eyasudev/-msft_button/ReadmeFiles/hardware-connection-images/hardware-camera-signal-1.jpeg

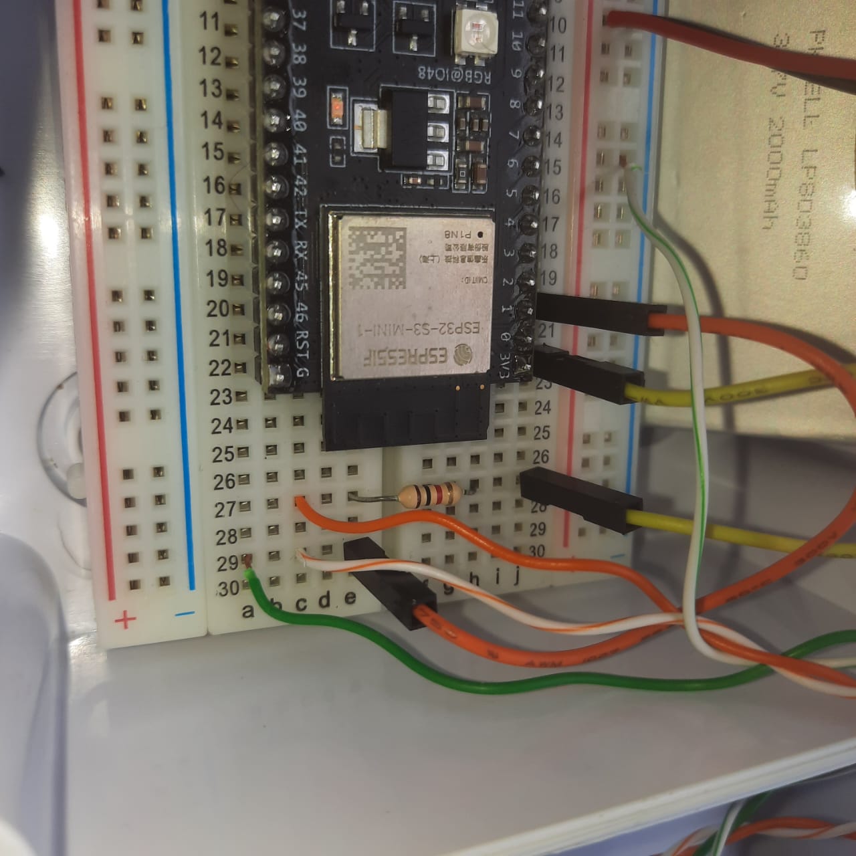
ReadmeFiles/hardware-connection-images/hardware-camera-signal-1.jpeg
