eyasudev/-msft_button/ReadmeFiles/hardware-connection-images/hardware-camera-signal-close-up.jpeg

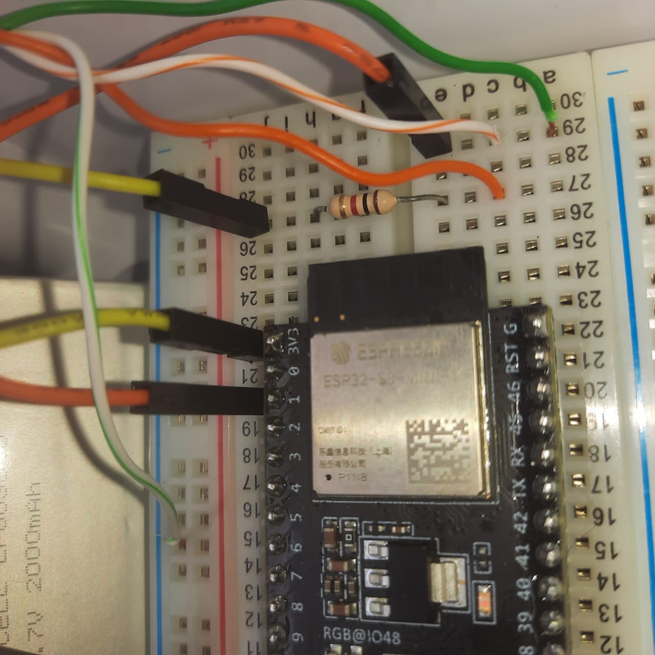
ReadmeFiles/hardware-connection-images/hardware-camera-signal-close-up.jpeg
