eyasudev/-msft_button/ReadmeFiles/hardware-connection-images/hardware-camera-top-of-cover.jpeg

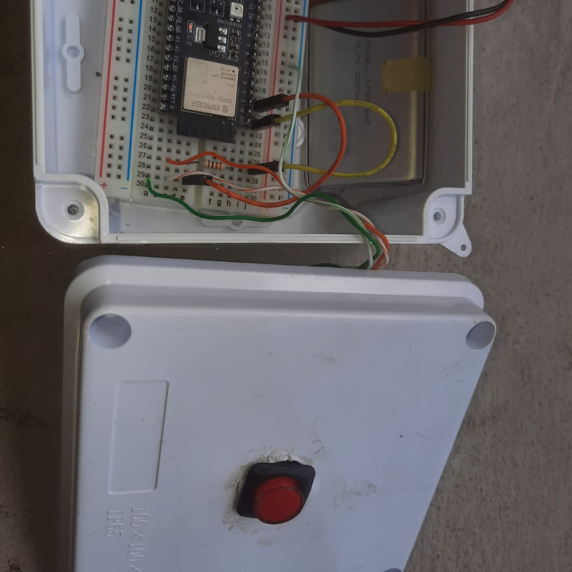
ReadmeFiles/hardware-connection-images/hardware-camera-top-of-cover.jpeg
