eyasudev/-msft_button/ReadmeFiles/v2 cable.webp

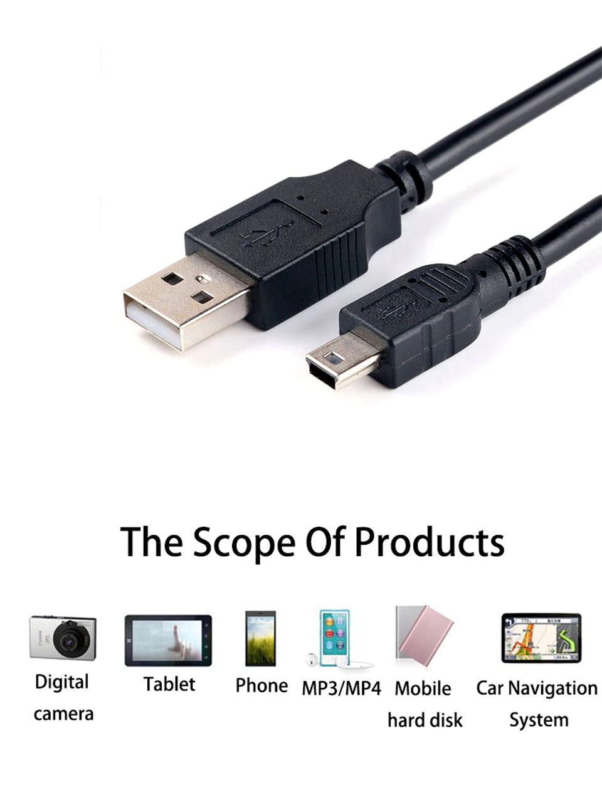
ReadmeFiles/v2 cable.webp
